Davidshao-114514/chuangkexunlianying/docs/07-教学设计说明.md

# 07 · 教学设计说明（给教师 / 社团讲师）

> 本学习包可作为 **2 学分 / 16–24 学时** 的项目式课程使用，也可裁成社团工作坊（4–8 学时）。
> 已按最终硬件与「9 模块（含踩坑复盘）」更新。

---

## §1 适用对象与先修

| 项 | 要求 |
|---|---|
| 面向 | 电子/自动化/机电/物理等专业大二及以上；或社团里有 C 语言基础的同学 |
| 先修 | C 语言基础、会看简单电路图、会用电烙铁 |
| 不需先修 | 不需要学过 MCU；不需要会 SolidWorks（STEP 直接打印） |
| 设备 | 每组：PCB 套件 1 套、3D 打印件（含按键帽）1 套、SWD 调试器、万用表、电烙铁、稳压电源（做电池保护测试） |

---

## §2 课时安排（16 学时标准版）

| 次 | 学时 | 内容 | 对应模块 | 课后任务 |
|---|---|---|---|---|
| 1 | 4 | 整机概览与供电设计；焊接训练（从主控开始） | 模块 1–2 | 完成 PCBA 焊接并通电初检 |
| 2 | 4 | 按键复合语义；PWM 调光（含手机拍频闪实验） | 模块 3–4 | 3 键全功能通过；频闪对比记录 |
| 3 | 4 | 磁吸检测与安全联动；采样与过放保护状态机 | 模块 5–6 | 吸附联动验收；保护阈值实测 |
| 4 | 4 | 低功耗与掉电记忆；结构装配与完整验收 | 模块 7–8 | 提交 14 项验收记录表 |
| 机动 | 2 | **踩坑复盘**（挑 1 个坑人为复现 + 写自己的记录） | 模块 9 | 提交 1 条踩坑记录（可 PR 进仓库） |

**精简版（社团工作坊 8 学时）**：合并 1–2（2h）、3–4（2h）、5–6（2h）、7–9（2h）；
焊接改为「教师预焊难点 + 学生焊常规件」。

**软件专修版（10–12 学时）**：跳过焊接（用已焊好的板），深挖模块 3–7 与 9，另加两个进阶题：
① 扩展 Flash 记忆支持跨午夜（增加日期字段）；② 把 `ApplyOutputs()` 的输出条件改造成显式状态机并写测试。

---

## §3 教学检查点（分阶段验收）

| 检查点 | 时点 | 验收内容 | 不通过的补救 |
|---|---|---|---|
| CP1 通电 | 第 1 次课后 | 3V3 轨受 CE 控制、SWD 可连接、屏点亮并显示电压 | 按 `docs/05` §6 排错表逐条排查 |
| CP2 交互 | 第 2 次课后 | 3 键全功能（单击/长按/双击）、两路独立调光、无频闪实验记录 | 重点查按键有效电平、去抖、占空比换算 |
| CP3 安全 | 第 3 次课后 | 吸附联动（脱落即灭）、未吸附不输出、电量误差 ≤±3%、过放保护阈值正确 | 查 DET 下拉、BGR 反推、滞回与 2s 确认 |
| CP4 整机 | 第 4 次课后 | 关机电流显著降低、唤醒不花屏、亮度记忆生效、温升与续航达标 | 查唤醒沿、延迟初始化、吞咽窗口、Flash 记录 |
| CP5 复盘 | 机动课时 | 能讲清 ≥3 个踩坑的根因；提交 1 条自己的踩坑记录 | 引导回到 `docs/08` 的「现象→假设→验证→结论」四段法 |

---

## §4 评分建议（百分制）

| 维度 | 权重 | 评分要点 |
|---|---|---|
| **功能实现** | 30% | `docs/06` §2 中与功能相关的项目（#1/#3/#4/#6/#7/#12）全通 |
| **数据与记录** | 20% | 14 项验收记录表：条件、原始数据、结论齐全；失败项有排查过程 |
| **原理理解** | 20% | 口试/笔试 3–5 问，例如：「为什么电池直供就不能用分压测电压？」「为什么最终选 8kHz？」「检测去抖为什么比按键长？」「Flash 记忆的时间窗解决了什么问题？」 |
| **工程规范** | 10% | 焊接质量、走线整理、代码是否符合 `docs/04` §12 约定 |
| **踩坑复盘** | 10% | 提交 1 条可复现的踩坑记录（现象/根因/解决/验证），或对 `docs/08` 的修正补充 |
| **共建贡献** | 10% | 提交 1 项可复现改进（新外壳/新功能/替代件验证/文档修正），说明验证方式 |

> 鼓励「失败但记录完整」：有失败项与排查过程的记录，比「一切正常」的空白表格得分更高。

---

## §5 常见教学陷阱（教师视角）

| 陷阱 | 现象 | 预防做法 |
|---|---|---|
| 学生跳过「为什么」 | 会烧录但不理解设计 | 每次课留 10 分钟口头答辩（§4 的问题库） |
| 只做软件、不懂电源 | 关机电流巨大仍以为正常 | 「关机电流」设为硬性检查点（CP4） |
| 照抄分压测压法 | 电池直供下读数恒定，学生以为代码错 | 先讲 `docs/08` §3.2 的因果链，再动手 |
| 认为频率越高越好 | 频闪/啸叫找不到原因 | 保留 1kHz 对照实验 + 查驱动手册区间 |
| 统一去抖时间 | 磁吸检测误判闪烁 | 对比按键 15ms 与检测 100ms，讲「时间由物理过程定」 |
| 忽视唤醒时序 | 花屏/松手重启反复出现 | 用 `docs/08` §3.4 的四个坑做引导式排查 |
| 依赖特定料号 | 换替代件后翻车 | 明确「哪些参数不可动」（`docs/03` §8） |
| 结构件装不上 | 打印公差 + 后处理不足 | 提供公差经验值（`docs/03` §9），预留修整时间 |

---

## §6 可扩展的教学项目（在完成本包后）

1. **加传感器**：光敏/距离 → 自动调光策略（保留手动覆盖）；
2. **加上报**：UART/蓝牙 → 亮度、电量、吸附状态上报（工位数字化类项目基础）；
3. **扩展记忆**：Flash 记录结构加日期字段，解决跨午夜过期问题；
4. **结构挑战**：在「吸附力不降」前提下减重 30%；
5. **成本挑战**：BOM 压 10% 且保持全部指标（替代件与供应链课题）；
6. **移植挑战**：把 `main.c` 语义移植到另一种 MCU（分层设计的真正检验）。

---

## §7 教学资源清单（本包已含）

| 资源 | 位置 |
|---|---|
| 讲义正文（9 模块） | `docs/02-学习路径.md` |
| 系统框图（可打印） | `docs/系统框图.png` |
| 原理图 / PCB 工程 | `工程文件夹/TYPE-A.epro2` |
| 固件源码（12 个 BSP 模块） | `USER/`、`MDK/` |
| 结构模型（含按键帽） | `工程文件夹/3D外壳/` |
| 最终配置与开发历程原文 | `工程文件夹/UserApp/DEVELOPMENT_SUMMARY.md` |
| **踩坑实录（最佳课堂素材）** | `docs/08-开发踩坑实录.md` |
| 测试判据与记录表 | `docs/06-测试与验收.md` |
| 复现与排错指南 | `docs/05-复现指南.md` |
