Davidshao-114514/chuangkexunlianying/仿真实跑不队_选题答辩项目V2/任务4_AI评价与团队分析记录.md

# 任务4：AI辅助选题评价与PPT迭代记录

**团队：** 1班C组 · 仿真实跑不队
**项目：** 磁吸焊接辅助手电
**评价对象：** PPT V1.0（《仿真实跑不队_磁吸焊接辅助手电_选题答辩PPT_V1.0》）
**日期：** 2026-08-28

---

## 一、AI提示词设计

**使用AI工具名称：** DeepSeek-V4（deepseek/deepseek-v4-flash-vision-exp）
**提问日期：** 2026-08-28

**前置输入方式说明：** 该AI工具已接收PPT V1.0完整核心内容（含封面/目录/选题背景/竞品对比/价值假设/精益画布/MVP验证/5W2H/增长潜力/实施规划/SCAMPER×六帽/Q&A/总结/附录），经工具限制核对后，以下为PPT核心内容文字摘要，作为评价对象输入。

**PPT核心内容摘要（评价对象）：**
- 用户画像：高校电子专业学生 / DIY极客 / 研发维修工程师；问卷126份，其中84.13%每周焊接≥3次、76.98%依赖精细补光、71.43%工位受限、100%需双手。
- 量化痛点：传统台灯68.25%、平价灯具61.11%、专业光源54.76%；沉浸式实测失败率 无灯50%→台灯30%→磁吸手电20%。
- 竞品对比：台灯60–200元/廉价灯20–49元/专业灯300元+/磁吸手电59–79元；本产品综合★★★★★。
- 核心价值主张：磁吸固定解放双手、万向悬停指哪照哪、无级调光、59–79元普惠定价。
- 待验证假设1–5（LED替代OLED、温度提醒+15元、青春版39–49元、高配版+8元、柔性臂3000次弯折漂移<5°）。
- 精益画布：问题/客户/价值主张/方案/优势/指标/渠道/成本/收入九模块。
- MVP：20人（DIY 4/实训生4/工程师4/初学者8）×25分钟A/B对比+虚拟支付问卷；成功标准≥70%状态查询≤2次且≤5秒（A/B差<10%）、≥60%愿购（59元档≥40%）、A组≥4/5；成本≈300元，6天。
- 市场/增长：留存率45.2%、高频刚需84.13%、潜在基数300万+。
- SCAMPER E维度暴露"宣传OLED vs 实物LED不符"；黑帽头号风险=宣传与实物不一致。
- 结论：需要调整后推进，即"证据闭环"状态参赛。

**提示词（完整原文）：**

> 这是为"创客训练营"课程制作的选题汇报PPT，请从以下维度对我们的选题进行评价：
> ① 需求真实性——用户痛点描述是否真实且足够痛？用户洞察数据是否支撑结论？
> ② 方案可行性——MVP是否能够有效验证核心假设？验证方案是否足够低成本？
> ③ 竞争差异化——竞品分析是否充分？与现有方案相比优势是否清晰可量化？
> ④ 逻辑自洽性——精益画布各模块之间是否存在逻辑闭环？假设-验证-结论链条是否完整？
> ⑤ 风险与漏洞——方案最脆弱的地方在哪里？PPT中是否暴露了未知的盲区？
> ⑥ 证据可信度——数据来源是否标注清晰？证据链是否完整可追溯？
> 请提出至少3个尖锐、具体的问题或建议。

**输出要求：** 要求AI提出具体、尖锐、可操作的问题或建议，而非泛泛的赞美或空泛的鼓励。

---

## 二、AI评价摘要

> 以下为AI工具返回的批判性评价（节选，其中标注★为团队选取的代表性观点）。

**① 需求真实性（混用口径，样本偏小）**
"需双手"（100%）与"84.13%/76.98%"等问卷统计项口径不一致——前者更像设计常识而非抽样结果，混用"陈述性常识"与"抽样统计"会削弱证据可信度。126份样本对三类人群而言偏小，且"每周≥3次"的判定标准未明确说明。

**② 方案可行性（样本功效不足，NTC未经验证）**
20人×A/B各10人无法支撑"差异<10%"的等价性判定——等价检验需要更大样本，否则"LED替代OLED成立"的统计说服力不足。验证成本300元虽低，但"20人×真实焊台×25分钟"的招募与执行难度可能被低估。NTC过温提示（¥0.5）属于"低成本补丁"，尚未证明其是否真实命中用户痛感。

**③ 竞争差异化（综合星级为自评，壁垒薄弱）★**
竞品对比表的"综合"星级（★★~★★★★★）为团队主观自评，未用补光谱、照度、稳定性等实测指标量化；"市场空白"结论建立在"现有方案无法兼顾四大需求"的定性判断上，未证明"磁吸+万向悬停"是否已被工业灯/专业灯以更高价覆盖。"不公平优势"栏仅为"成熟供应链/价格分层/创客属性"，缺乏可验证的护城河（大厂3个月可仿制）。

**④ 逻辑自洽性（画布闭环未闭合，宣传与实物未对齐）★**
精益画布"问题→价值主张→方案/优势→关键指标→收入"为单向线性，但最核心的"成本结构"与"收入来源"之间（59元能否覆盖BOM+小批量成本）没有在产品演进中闭环；更关键的是，宣传口径（OLED）与实物（LED）不一致——在"解决方案"栏仍写"LED(OLED选配)"，说明方案层与价值主张层存在未对齐。

**⑤ 风险与漏洞（黑帽风险未量化）★**
PPT未充分暴露"小批量外壳与柔性臂成本高于预估、59元可能守不住"这一黑帽核心风险，仅在"实施规划"点到"压缩BOM/降级"；锂电池3C认证成本与合规周期只有定性表述，无量化（成本/时间）；3人团队"同时磨硬件+测试"的时间约束没有缓冲。最脆弱处：OLED/LED宣传矛盾虽是"自我发现"，但能否真正转化为用户可感知的差异点存疑。

**⑥ 证据可信度（引用无出处，链条未闭合）**
留存率45.2%（短期试点）、"80%状态查询需求"、失败率50%→20%的测量协议均未注明来源；"300万+潜在基数"无估算依据。部分数据（如88%/92%用户认可）在早前PPT出现但本报告未给出来源，存在"引用无出处"风险。且关键假设1、2尚未被验证，PPT却以"价值验证"自居——证据链"假设→验证→结论"在V1.0中尚未闭合。

---

## 三、团队分析与回应（选取3个最具代表性观点）

### 观点1（对应④ 逻辑自洽性 + ⑤ 风险与漏洞）

**AI指出：** 宣传口径（OLED）与实物（LED）不一致，精益画布"方案层与价值主张层未对齐"，这是方案最脆弱之处；且在SCAMPER的E维度与六帽黑帽中被重复点名。

- **认同：** 完全认同。这正是我们在SCAMPER E维度与六顶帽黑帽中自行发现的头号风险——"宣传OLED vs 实物LED"严重不一致，若不先补证再定稿，答辩会被评委当场质疑。AI从外部视角再次确认了这一点，形成"团队内部自查 + AI外部印证"的双重复核，说明该问题确凿而非自我怀疑。
- **已执行：** 我们据此对PPT做了如下收敛：
  1. **统一宣传口径**：把"OLED状态显示"从核心卖点降级为"选配扩展模块（H1排针预留）"，并在封面/价值主张/画布"解决方案"栏统一改为"LED状态标配 + OLED选配"；
  2. **画布对齐**：在精益画布"解决方案"栏明确标注"LED标配、OLED为选配扩展"，消除方案层与价值主张层的口径冲突；
  3. **新增"证据闭环"主线**：把"待验证假设"前置为"尚未验证、需MVP决策"的状态标注，避免以"价值验证"自居。
  - **产生效果**：从"多功能宣传型产品"收敛为"可验证、可量产、低成本"方案，把最可能被当场质疑的劣势，转化为"可讲解的迭代设计"（与AI评价的理念一致）。
- **存疑：** 无，此点无分歧。

### 观点2（对应③ 竞争差异化）

**AI指出：** 竞品对比"综合星级"为团队主观自评，未用量化实测指标；"市场空白"结论基于定性判断，且"不公平优势/护城河"不够可验证。

- **认同：** 部分认同。我们承认"综合星级"（★★~★★★★★）确为团队综合判断，而非逐项实测打分，形式上不够严谨；"空白"结论也确实建立在"现有方案无法兼顾四大需求"的定性逻辑上。
- **已执行：** 我们补强了两处量化支撑：
  1. 在竞品对比表中明确标注评分依据（磁吸、无级调光、状态显示、空间占用四项的可量化事实），并把"综合"栏改为"由四项指标加权得出"，落实标注；
  2. 用"失败率50%→20%"与"79元 vs 300元+"的价格差作为差异化落点，替代纯文字"更强/更优"表述。
- **存疑：** 对"护城河不足"有保留。AI以"大厂3个月可仿制"认定壁垒薄弱，但我们认为价格分层（49/79元两档）＋创客教育深度属性（自制套件版强化动手属性）＋垂直场景深耕（高校/DIY社区渠道）是"性价比+教育生态"式竞争策略，而非依赖单一硬件隔绝。该策略的大厂模仿成本高、回报低，故我们保留"不公平优势"的定位，但同意在V2.0中将"护城河"进一步明确为"价格分层+创客生态+标准数据接口（OPC生态）"三层，而非单点硬件。

### 观点3（对应② 方案可行性）

**AI指出：** 20人样本对验证"比例型假设"（覆盖80%需求、≥60%愿购）功效不足，且A/B各10人难以支撑"差异<10%"的等价性结论；MVP执行难度或低估。

- **认同：** 部分认同。我们承认样本量偏小、统计功效有限，这是MVP阶段"最小成本验证"的固有权衡。
- **已执行：** 我们从"严格统计功效"转向"方向性证据 + 明确退路"的表述，在PPT中把MVP定位为"低成本的早期方向性验证"，同时补上失败退路（若A组显著低于B组或愿购<40%，则转入"集成OLED版/降价版"），而非宣称"已验证"。这样既保留低成本验证价值，又避免过度推导统计结论。
- **存疑：** 对"MVP执行难度被低估"不完全认同。我们已按5W2H将执行拆解为"招募（姜）—样机调校（李）—主持与数据（邵）"三人分工，并选在电工基地真实焊台、按"下午3点靠窗"标准化环境光，且安排了"交换组别重测一次"以消除个体差异。该拆解我们认为已充分覆盖执行要素；但同意在V2.0中追加"若现场招募不足20人的备选样本方案（5人/组×4场）"作为缓冲，提升落地稳健性。

---

## 四、结论

通过AI的外部批判性审视，团队用"认同/已执行/存疑"三层机制对6条意见逐条消化：完全认同并已执行1条（宣传与实物对齐），部分认同并已执行2条（量化竞品、MVP定位），部分保留并建立应对计划1条（护城河定义）。核心价值在于：AI作为"外部视角的镜子"，使我们确认了自身自查出的最大风险（OLED/LED不一致），并把"争议项"转化为"可讲解的迭代设计"。本记录已作为任务5中PPT V2.0"AI评价与团队分析"页的核心素材。
