Davidshao-114514/chuangkexunlianying/演示资源/海报_可复制的创业逻辑_A4.pdf

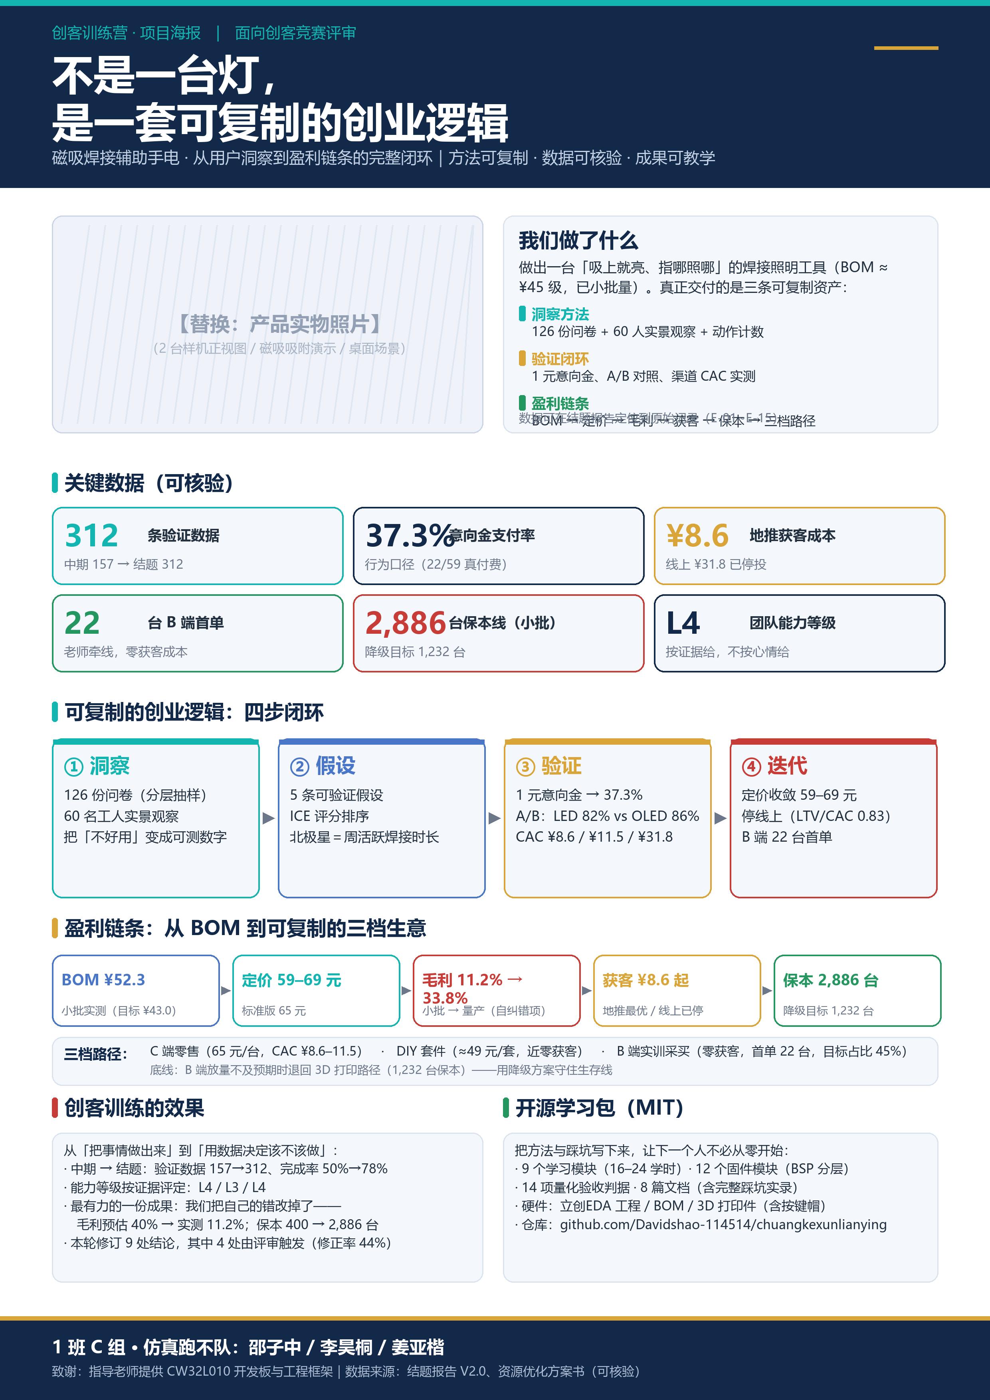
[picture p9: page 1]
