Davidshao-114514/chuangkexunlianying/创客训练营-2026第1课课前任务/倾听思维导图.png

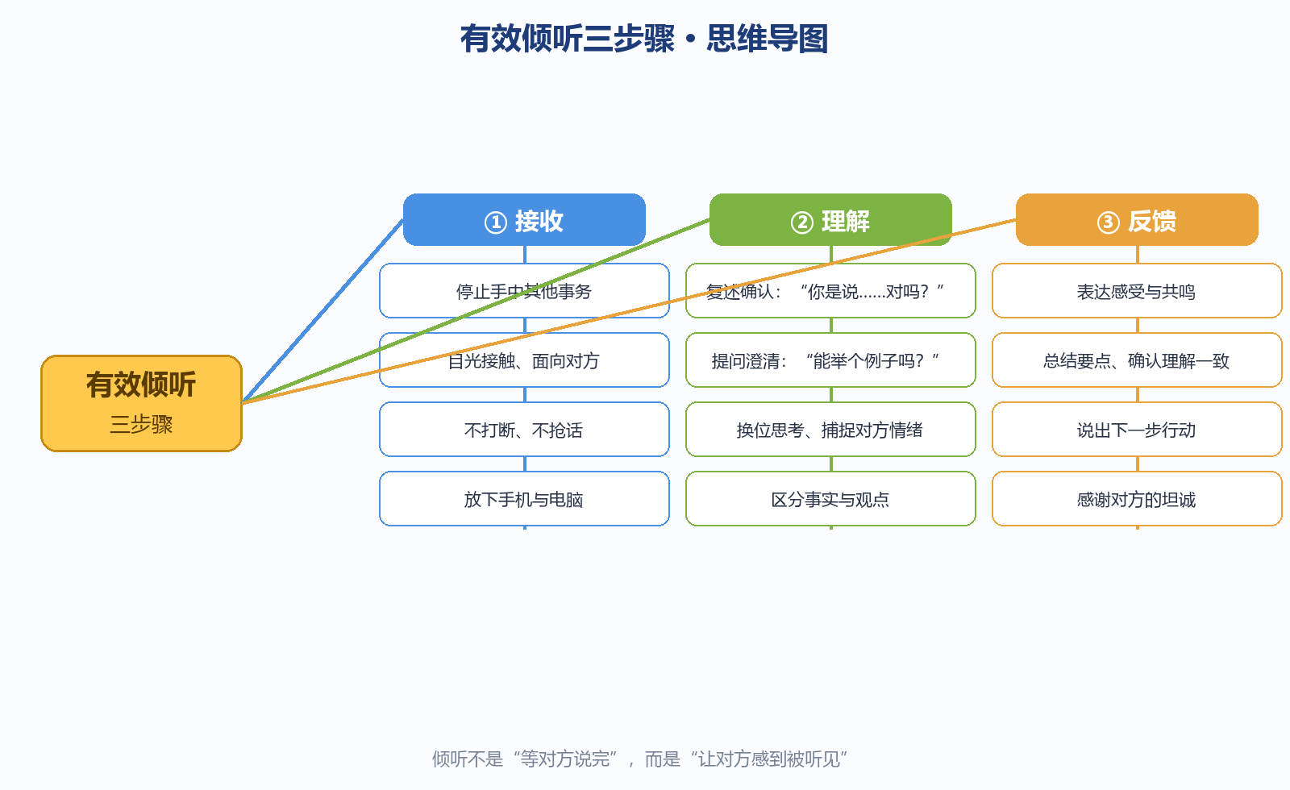
创客训练营-2026第1课课前任务/倾听思维导图.png
