Davidshao-114514/chuangkexunlianying/创客训练营-2026第1课课前任务/海报-团队招募.png

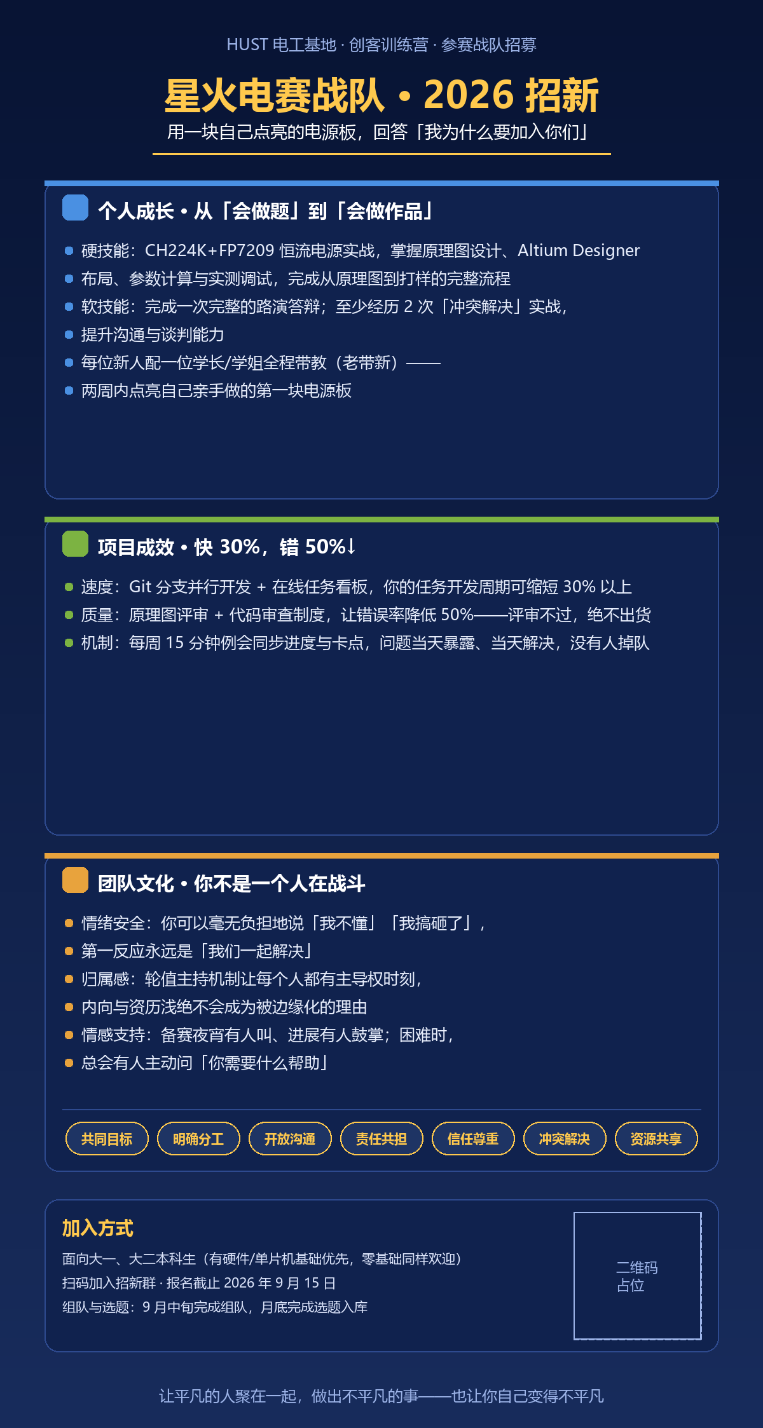
创客训练营-2026第1课课前任务/海报-团队招募.png
