Davidshao-114514/chuangkexunlianying/创客训练营-2026第1课课前任务/电子名片.png

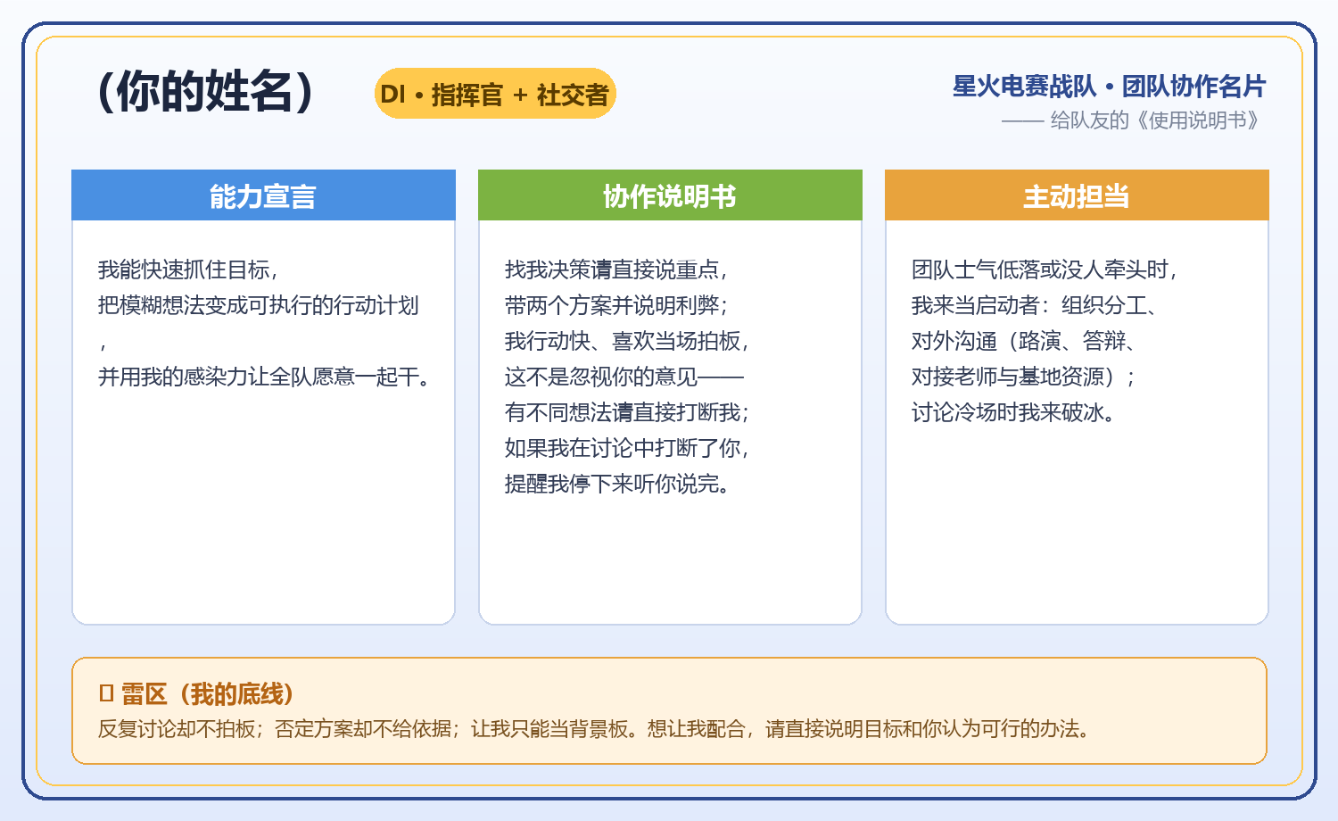
创客训练营-2026第1课课前任务/电子名片.png
