Davidshao-114514/chuangkexunlianying/创新方法工作坊-课前任务/创新方法vs设计思维-思维导图.png

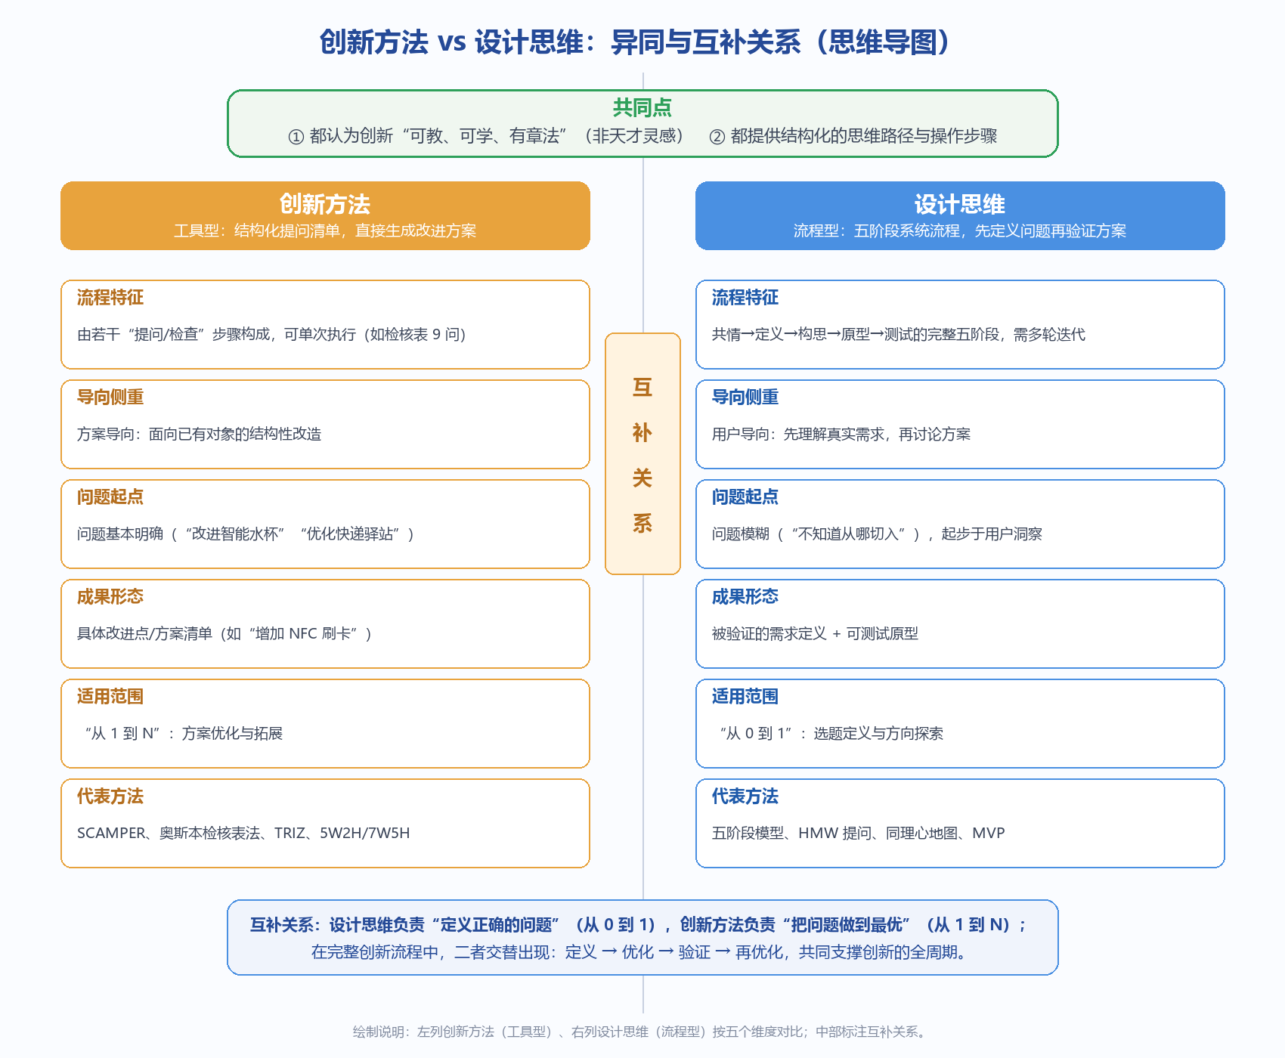
创新方法工作坊-课前任务/创新方法vs设计思维-思维导图.png
