Davidshao-114514/chuangkexunlianying/泡茶项目管理方案/_bot.png

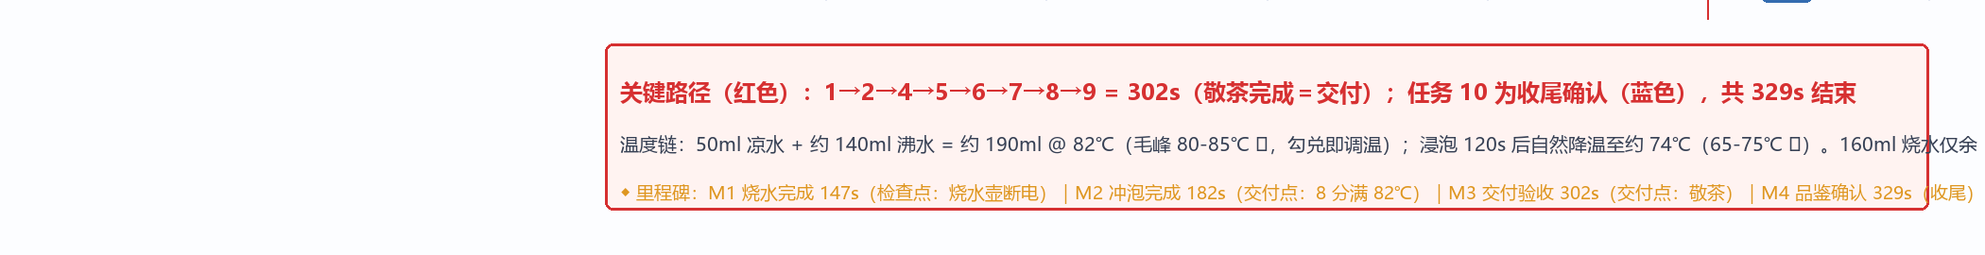
泡茶项目管理方案/_bot.png
