Davidshao-114514/chuangkexunlianying/泡茶项目管理方案/_top.png

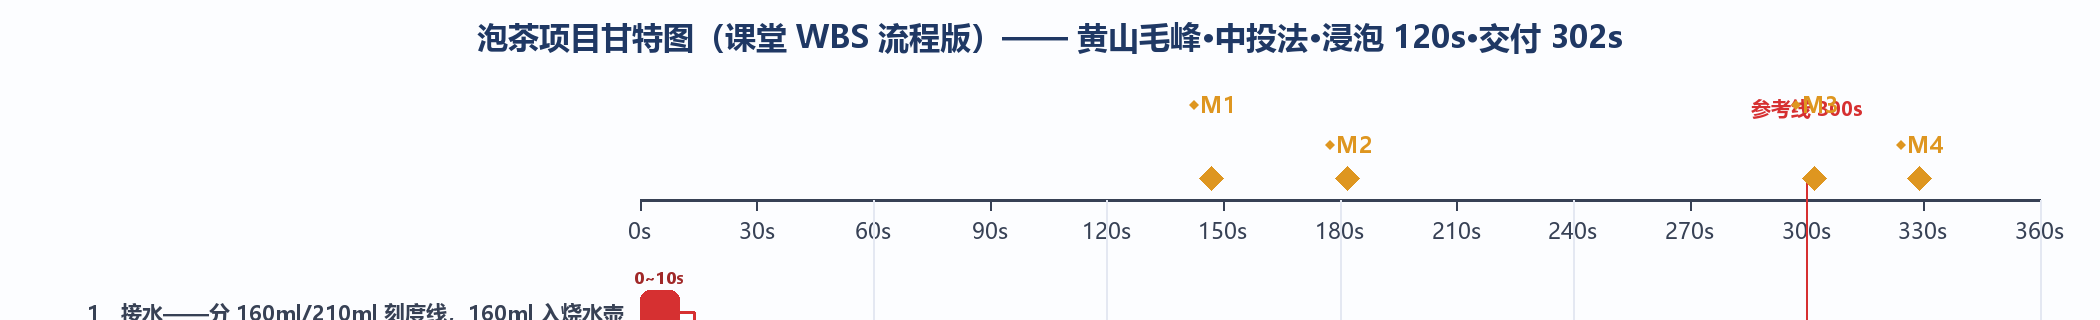
泡茶项目管理方案/_top.png
