Davidshao-114514/chuangkexunlianying/泡茶项目管理方案/泡茶项目甘特图-黄山毛峰版.png

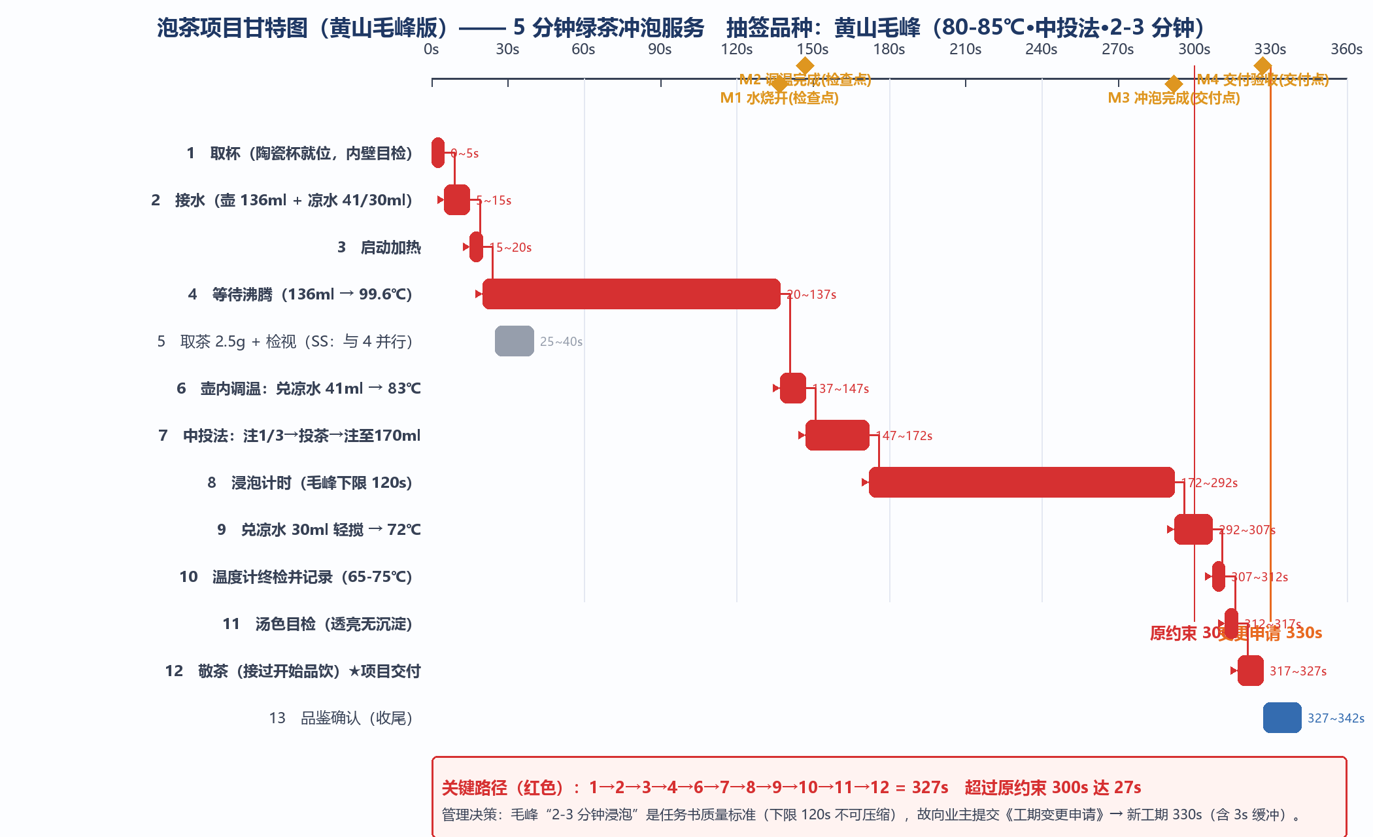
泡茶项目管理方案/泡茶项目甘特图-黄山毛峰版.png
