Davidshao-114514/chuangkexunlianying/设计思维工作坊-课前任务/设计思维五阶段模型图.png

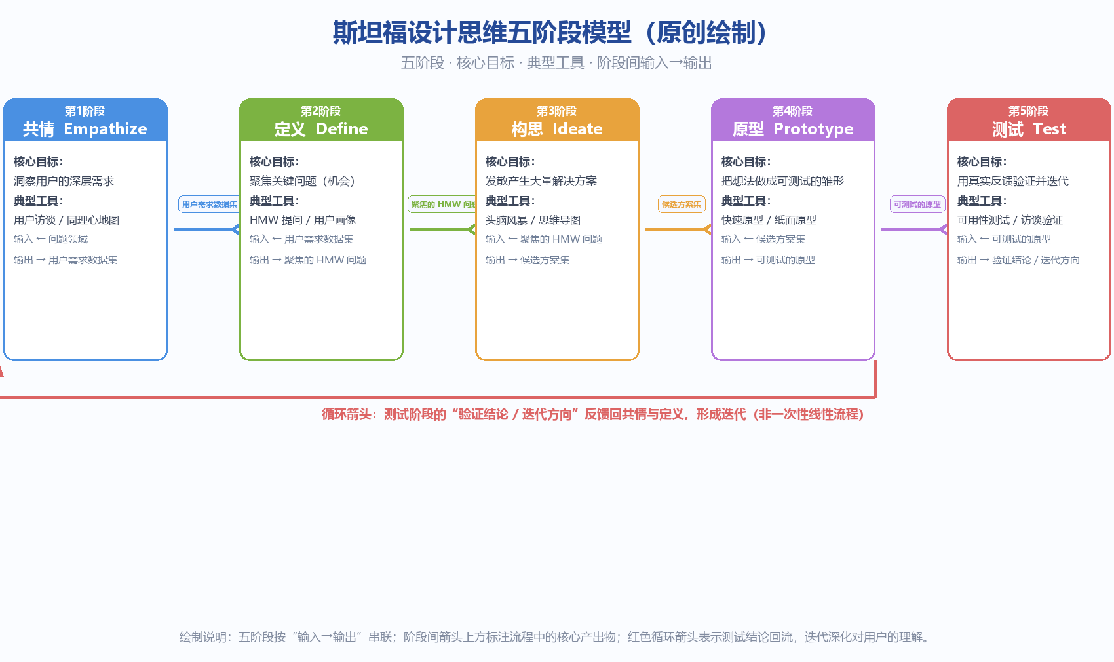
设计思维工作坊-课前任务/设计思维五阶段模型图.png
