Davidshao-114514/chuangkexunlianying/USER/src/bsp_oled_text.c

#include "bsp_oled_text.h"

/* Chinese 16x16 glyphs (index n, n<8) */
const unsigned char F16x16[] =
{
	0,0,252,36,36,228,36,36,34,34,34,163,98,0,0,0,
	64,48,143,128,64,64,35,20,8,20,34,65,64,128,128,0,
	64,48,143,8,40,24,64,92,84,84,127,84,84,92,64,0,
	0,0,127,32,16,8,128,159,65,33,29,33,65,159,0,0,
	0,0,248,136,136,136,136,255,136,136,136,136,248,0,0,0,
	0,0,31,8,8,8,8,127,136,136,136,136,159,128,240,0,
	0,0,254,2,130,130,130,130,250,130,130,130,130,130,2,0,
	128,96,31,64,64,64,64,64,127,64,64,68,88,64,64,0,
	0,0,252,36,36,228,36,36,34,34,34,163,98,0,0,0,
	64,48,143,128,64,64,35,20,8,20,34,65,64,128,128,0,
	64,48,143,8,40,24,64,92,84,84,127,84,84,92,64,0,
	0,0,127,32,16,8,128,159,65,33,29,33,65,159,0,0,
	0,0,248,136,136,136,136,255,136,136,136,136,248,0,0,0,
	0,0,31,8,8,8,8,127,136,136,136,136,159,128,240,0,
	16,96,2,140,0,68,100,84,77,70,68,84,100,196,4,0,
	4,4,126,1,128,64,62,0,0,254,0,0,126,128,224,0,
};

/* ASCII 6x8 (index = char-32) */
const unsigned char F6x8[][6] =
{
	0,0,0,0,0,0,
	0,0,0,47,0,0,
	0,0,7,0,7,0,
	0,20,127,20,127,20,
	0,36,42,127,42,18,
	0,98,100,8,19,35,
	0,54,73,85,34,80,
	0,0,5,3,0,0,
	0,0,28,34,65,0,
	0,0,65,34,28,0,
	0,20,8,62,8,20,
	0,8,8,62,8,8,
	0,0,0,160,96,0,
	0,8,8,8,8,8,
	0,0,96,96,0,0,
	0,32,16,8,4,2,
	0,62,81,73,69,62,
	0,0,66,127,64,0,
	0,66,97,81,73,70,
	0,33,65,69,75,49,
	0,24,20,18,127,16,
	0,39,69,69,69,57,
	0,60,74,73,73,48,
	0,1,113,9,5,3,
	0,54,73,73,73,54,
	0,6,73,73,41,30,
	0,0,54,54,0,0,
	0,0,86,54,0,0,
	0,8,20,34,65,0,
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
	8,248,136,136,136,112,0,0,32,63,32,32,32,17,14,0,
	192,48,8,8,8,8,56,0,7,24,32,32,32,16,8,0,
	8,248,8,8,8,16,224,0,32,63,32,32,32,16,15,0,
	8,248,136,136,232,8,16,0,32,63,32,32,35,32,24,0,
	8,248,136,136,232,8,16,0,32,63,32,0,3,0,0,0,
	192,48,8,8,8,56,0,0,7,24,32,32,34,30,2,0,
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
};
