Davidshao-114514/chuangkexunlianying/USER/src/interrupts_cw32l010.c

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

/* Includes ------------------------------------------------------------------*/
#include "../inc/interrupts_cw32l010.h"
#include "../inc/main.h"
#include "cw32l010_btim.h"
/* External variables --------------------------------------------------------*/
/******************************************************************************/
/*           Cortex-M0P Processor Interruption and Exception Handlers          */
/******************************************************************************/
/**
  * @brief This function handles Non maskable interrupt.
  */
void NMI_Handler(void)
{
}

/**
  * @brief This function handles Hard fault interrupt.
  */
void HardFault_Handler(void)
{
    while (1)
    {
    }
}


/**
  * @brief This function handles System service call via SWI instruction.
  */
void SVC_Handler(void)
{
}


/**
  * @brief This function handles Pendable request for system service.
  */
void PendSV_Handler(void)
{
}


/******************************************************************************/
/* CW030 Peripheral Interrupt Handlers                                        */
/* Add here the Interrupt Handlers for the used peripherals.                  */
/* For the available peripheral interrupt handler names,                      */
/* please refer to the startup file (startup_ps030.s).                        */
/******************************************************************************/

/**
 * @brief This funcation handles WDT
 */
void WDT_IRQHandler(void)
{
    /* USER CODE BEGIN */

    /* USER CODE END */
}

/**
 * @brief This funcation handles LVD
 */
void LVD_IRQHandler(void)
{
    /* USER CODE BEGIN */

    /* USER CODE END */
}

/**
 * @brief This funcation handles RTC
 */
void RTC_IRQHandler(void)
{
    /* USER CODE BEGIN */

    /* USER CODE END */
}

/**
 * @brief This funcation handles FLASHRAM
 */
void FLASHRAM_IRQHandler(void)
{
    /* USER CODE BEGIN */

    /* USER CODE END */
}

/**
 * @brief This funcation handles SYSCTRL
 */
void SYSCTRL_IRQHandler(void)
{
    /* USER CODE BEGIN */

    /* USER CODE END */
}

/**
 * @brief This funcation handles GPIOA
 * 正常运行时作按键中断(未启用); 停机模式下为唤醒中断源, 唤醒后清零标志即可
 */
void GPIOA_IRQHandler(void)
{
    /* 清除所有已置位的中断标志 (写0清零, 见 GPIOA_INTFLAG_CLR) */
    if (CW_GPIOA->ISR != 0)
        GPIOA_INTFLAG_CLR(CW_GPIOA->ISR);
}

/**
 * @brief This funcation handles GPIOB
 */
void GPIOB_IRQHandler(void)
{
    if (CW_GPIOB->ISR != 0)
        GPIOB_INTFLAG_CLR(CW_GPIOB->ISR);
}


/**
 * @brief This funcation handles ADC
 */
void ADC_IRQHandler(void)
{
    /* USER CODE BEGIN */

    /* USER CODE END */
}

/**
 * @brief This funcation handles ATIM
 */
void ATIM_IRQHandler(void)
{
    /* USER CODE BEGIN */

    /* USER CODE END */
}

/**
 * @brief This funcation handles VC1
 */
void VC1_IRQHandler(void)
{
    /* USER CODE BEGIN */

    /* USER CODE END */
}

/**
 * @brief This funcation handles VC2
 */
void VC2_IRQHandler(void)
{
    /* USER CODE BEGIN */

    /* USER CODE END */
}

/**
 * @brief This funcation handles GTIM1
 */
void GTIM1_IRQHandler(void)
{
    /* USER CODE BEGIN */

    /* USER CODE END */
}

/**
 * @brief This funcation handles LPTIM
 */
void LPTIM_IRQHandler(void)
{
    /* USER CODE BEGIN */

    /* USER CODE END */
}

/**
 * @brief This funcation handles BTIM1
 * 1ms 周期中断: 作为系统时基, 驱动按键扫描/ADC采样/界面刷新等周期任务
 */
void BTIM1_IRQHandler(void)
{
    /* 确认 BTIM1 更新中断 */
    if (BTIM_GetITStatus(CW_BTIM1, BTIM_IT_UPDATE) == SET)
    {
        /* 清中断标志 */
        BTIM_ClearITPendingBit(CW_BTIM1, BTIM_IT_UPDATE);

        /* 周期任务(在 main.c 中实现, 内部按 1ms/5ms/50ms/200ms 分频调度) */
        App_Task1ms();
    }
}

/**
 * @brief This funcation handles BTIM2
 */
void BTIM2_IRQHandler(void)
{
    /* USER CODE BEGIN */

    /* USER CODE END */
}

/**
 * @brief This funcation handles BTIM3
 */
void BTIM3_IRQHandler(void)
{
    /* USER CODE BEGIN */

    /* USER CODE END */
}

/**
 * @brief This funcation handles I2C1
 */
void I2C1_IRQHandler(void)
{
    /* USER CODE BEGIN */

    /* USER CODE END */
}

/**
 * @brief This funcation handles SPI1
 */
void SPI1_IRQHandler(void)
{
    /* USER CODE BEGIN */

    /* USER CODE END */
}

/**
 * @brief This funcation handles UART1
 */
void UART1_IRQHandler(void)
{
    /* USER CODE BEGIN */

    /* USER CODE END */
}

/**
 * @brief This funcation handles UART2
 */
void UART2_IRQHandler(void)
{
    /* USER CODE BEGIN */

    /* USER CODE END */
}


/**
 * @brief This funcation handles FAULT
 */
void CLKFAULT_IRQHandler(void)
{
    /* USER CODE BEGIN */

    /* USER CODE END */
}

/************************ (C) COPYRIGHT CW *****END OF FILE****/
